crodar33/CommandPoint/spi/can_a4_1.lua

--Frame 1 battery charge voltage, DC charge current limitation, DC discharge current limitation, Battery discharge voltage
local chargeV = 576 --3.60*16=57.6 - 2.81*16=44.96
local chargeA = 450 --
local dischargeA = 650
local cutFoffVoltage = 450
local SOC = struct.unpack("<h", struct.pack("H", battery.SOC))
local SOH = struct.unpack("<h", struct.pack("H", battery.SOH))


batTemp = struct.unpack("<h", struct.pack("H", battery.temp[1]*10))

--charge limits
if SOC >= 100 then
    chargeA = 0
elseif SOC>95 then
    chargeA = 50
elseif SOC>90 then
    chargeA = 100
elseif SOC>80 then
    chargeA = 150
end
--discharge limits
if SOC > 50 then
    dischargeA = 650
elseif SOC > 20 then
    dischargeA = 400
else
    dischargeA = 200
end

if (inverterCmdMod==3 and batTemp < 500) then
    chargeA = inverterMaxCurrent
    if (SOC > 90) then
        SOC = 90
    end
elseif (inverterCmdMod==3 and batTemp >= 500) then
    inverterCmdMod = 0
end

if ((batTemp > 500) ) then
    dischargeA = 0
elseif ((batTemp > 400) ) then
    dischargeA = dischargeA/2
end

if math.max(unpack(battery.cellVoltage))>3.60 then
    inveterChargeCorrection = 0
    chargeA = 20;
elseif math.max(unpack(battery.cellVoltage))>3.4 then
    inveterChargeCorrection = math.max(0, inveterChargeCorrection - 1)
    chargeA = 50 + math.ceil((chargeA - 50) * (inveterChargeCorrection / 10));
else
    inveterChargeCorrection = math.min(10, inveterChargeCorrection + 1)
end

if math.min(unpack(battery.cellVoltage))<2.6 then
    dischargeA = 0;
end

if (batTemp > 450) then
    chargeA = 0
elseif (batTemp > 400 and chargeA > 50) then
    chargeA = 50
end


local canBuss = require "can_module"
--print("Charge values: ", chargeV, chargeA)
sendStatus, sendFlag, msg = canBuss.sendCanMessage(0x0351, {
    struct.pack("<H", chargeV), 
    struct.pack("<H", chargeA), 
    struct.pack("<H", dischargeA), 
    struct.pack("<H", cutFoffVoltage)
})
package.loaded.can_module = nil
