crodar33/CommandPoint/spi/can_a4_3.lua

--frame 3, Battery voltage, Battery current, Battery Temperature, Cycles
local batV = struct.unpack("<h", struct.pack("H", battery.voltage * 100))
local batA = struct.unpack("<h", struct.pack("H", battery.current * 10))
local batC = struct.unpack("<h", struct.pack("H", battery.cicles))
print("V: ", batV, "A: ", batA, "C: ", batC, "T: ", batTemp)
--batA = 10
--batC = 100
local canBuss = require "can_module"
sendStatus, sendFlag = canBuss.sendCanMessage(0x0356, {
    struct.pack("<h", batV), --batt V
    struct.pack("<h", batA), --batt A
    struct.pack("<h", batTemp), --batt T
    struct.pack("<H", batC) -- batt Cicles
})
package.loaded.can_module = nil
