crodar33/CommandPoint/bms_daly/daly_read_soc.lua

return function(battery, sUart, RW_pin)

    local callback = function(data)
        if not chechCRC(data) then
            print("bad CRC 0x90")
            print("Response: ", dataToString(data)) 
            return
        end
        if (struct.unpack("B", data, 2)~=battery.address) then
            return
        end
        battery.last_update = tmr.time()
        battery.pressure = struct.unpack(">H", data, 5+0) / 10
        battery.acquisition = struct.unpack(">H", data, 5+2) / 10
        local curr = struct.unpack(">H", data, 5+4) / 10
        local soc = struct.unpack(">H", data, 5+6) / 10
        print("R: pressure ".. battery.pressure .. ", acquisition ".. battery.acquisition .. ", curr ".. curr .. ", soc ".. soc )
        battery.SOC = soc
        if battery.pressure>0 then
            battery.voltage = battery.pressure
        elseif battery.acquisition>0 then
            battery.voltage = battery.acquisition
        else           
            battery.voltage = 0
        end
        battery.current = curr - 3000
        battery.SOC = soc
    end
  
    --request new data
    local sendData = struct.pack(">BBBBBBBBBBBBB", 0xA5, 0x40, 0x90, 0x08, 0, 0, 0, 0, 0, 0, 0, 0, 0x7D)    
    --set callback on what we waiting
    --print("Requested: ", dataToString(sendData))
    sUart:on("data", 13, callback)
    --send data
    gpio.write(RW_pin, gpio.HIGH)
    sUart:write(sendData)
    gpio.write(RW_pin, gpio.LOW)

end
